microchip-pic-avr-examples/pic16f56q71-audio-light-show-mplab-mcc/images/ws2812_implementation.png

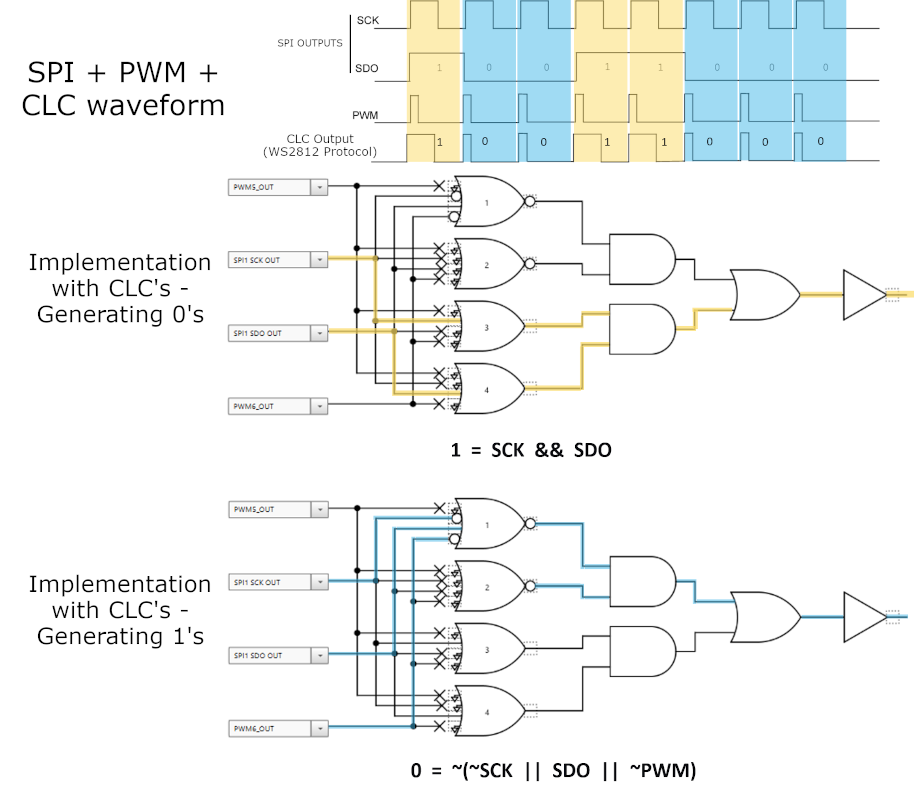
images/ws2812_implementation.png
